gildobjanschi/ECP5_BGA381_FT2232HQ_FIFO/hdl/tx.sv

/***********************************************************************************************************************
 * Copyright (c) 2024 Virgil Dobjanschi dobjanschivirgil@gmail.com
 *
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
 * THE SOFTWARE IS PROVIDED "AS IS", WITHOUT WARRANTY OF ANY KIND, EXPRESS OR IMPLIED, INCLUDING BUT NOT LIMITED TO THE
 * WARRANTIES OF MERCHANTABILITY, FITNESS FOR A PARTICULAR PURPOSE AND NONINFRINGEMENT. IN NO EVENT SHALL THE AUTHORS
 * OR COPYRIGHT HOLDERS BE LIABLE FOR ANY CLAIM, DAMAGES OR OTHER LIABILITY, WHETHER IN AN ACTION OF CONTRACT, TORT OR
 * OTHERWISE, ARISING FROM, OUT OF OR IN CONNECTION WITH THE SOFTWARE OR THE USE OR OTHER DEALINGS IN THE SOFTWARE.
 **********************************************************************************************************************/
`timescale 1ps/1ps
`default_nettype none

`include "definitions.svh"

module tx (
    input logic reset_i,
    input logic clk_24576000_i,
    input logic clk_22579200_i,
    // Input FIFO access
    output logic rd_in_fifo_clk_o,
    output logic rd_in_fifo_en_o,
    input logic rd_in_fifo_empty_i,
    input logic [7:0] rd_in_fifo_data_i,
    // Output FIFO ports
    output logic wr_out_fifo_clk_o,
    output logic wr_out_fifo_en_o,
    output logic [7:0] wr_out_fifo_data_o,
    input logic wr_out_fifo_full_i,
    input logic wr_out_fifo_afull_i,
    output logic led_test_mode
`ifdef EXT_ENABLED
    ,
    output logic ext_led_app_in_fifo_rd_o,
    output logic ext_led_app_out_fifo_wr_o,
    output logic ext_led_app_tx_err_o,
    output logic ext_led_test_ok,
    output logic ext_led_test_fail
`endif
    );

    logic clk;
    assign clk = clk_24576000_i;

    assign rd_in_fifo_clk_o = clk;
    assign wr_out_fifo_clk_o = clk;

`ifdef EXT_ENABLED
    assign ext_led_app_in_fifo_rd_o = rd_in_fifo_en_o;
    assign ext_led_app_out_fifo_wr_o = wr_out_fifo_en_o;
`endif

`ifndef DATA_PACKETS_COUNT
    `define DATA_PACKETS_COUNT 8'd1
`endif

`ifndef DATA_PACKET_PAYLOAD
    `define DATA_PACKET_PAYLOAD 6'd63
`endif

    // State machines
    localparam STATE_IDLE       = 3'b000;
    localparam STATE_RD         = 3'b001;
    localparam STATE_WR_BUFFER  = 3'b010;
    localparam STATE_WR         = 3'b011;
    localparam STATE_ERROR      = 3'b111;
    logic [2:0] state_m;

    // Protocol state machine
    localparam STATE_FIFO_CMD       = 1'b0;
    localparam STATE_FIFO_PAYLOAD   = 1'b1;
    logic fifo_state_m;

    logic [1:0] last_fifo_cmd;
    logic data_to_send;
    logic [5:0] rd_payload_bytes;
    logic [5:0] wr_data_index;
    logic [7:0] wr_data[0:3];

`ifdef TEST_MODE
    logic [7:0] test_number;
    logic [7:0] expected_test_data;
    logic [7:0] wr_packets;
    logic [5:0] wr_payload_bytes;

    //==================================================================================================================
    // The command handler
    //==================================================================================================================
    task handle_cmd_task (input logic [1:0] fifo_cmd, input logic [5:0] payload_length);
        (* parallel_case, full_case *)
        case (fifo_cmd)
            `CMD_TEST_START: begin
`ifdef EXT_ENABLED
                ext_led_test_ok <= 1'b0;
                ext_led_test_fail <= 1'b0;
`endif

                if (payload_length == 6'd1) begin
`ifdef D_TX
                    $display ($time, "\033[0;36m TX:\t--> CMD_TEST_START. \033[0;0m");
`endif
                    // Reset the test data
                    expected_test_data <= 8'd0;
                    data_to_send <= 1'b0;

                    rd_payload_bytes <= payload_length;
                    fifo_state_m <= STATE_FIFO_PAYLOAD;
                end else begin
`ifdef D_TX
                    $display ($time, "\033[0;36m TX:\t[ERROR] --> CMD_TEST_START payload bytes: %d (expected 1). \033[0;0m", payload_length);
`endif
                    wr_data_index <= 6'd0;
                    wr_data[0] <= {`CMD_TEST_STOPPED, 6'h1};
                    wr_data[1] <= `TEST_ERROR_INVALID_START_PAYLOAD;

                    rd_in_fifo_en_o <= 1'b0;
                    state_m <= STATE_ERROR;
                end
            end

            `CMD_TEST_DATA: begin
`ifdef D_TX
                $display ($time, "\033[0;36m TX:\t--> CMD_TEST_DATA payload bytes: %d. \033[0;0m", payload_length);
`endif
                if (payload_length > 6'd0) begin
                    rd_payload_bytes <= payload_length;
                    fifo_state_m <= STATE_FIFO_PAYLOAD;
                end
            end

            `CMD_TEST_STOP: begin
                wr_data_index <= 6'd0;
                wr_data[0] <= {`CMD_TEST_STOPPED, 6'h1};
                if (payload_length == 6'd0) begin
`ifdef D_TX
                    $display ($time, "\033[0;36m TX:\t--> CMD_TEST_STOP. \033[0;0m");
`endif
                    wr_data[1] <= `TEST_ERROR_NONE;

                end else begin
`ifdef D_TX
                    $display ($time, "\033[0;36m TX:\t[ERROR] --> CMD_TEST_STOP payload bytes: %d (expected 0). \033[0;0m", payload_length);
`endif
                    wr_data[1] <= `TEST_ERROR_INVALID_STOP_PAYLOAD;
                end

                rd_in_fifo_en_o <= 1'b0;
                state_m <= STATE_ERROR;
            end

            default: begin
`ifdef D_TX
                $display ($time, "\033[0;36m TX:\t[ERROR] --> invalid command: %d. \033[0;0m", fifo_cmd);
`endif
                wr_data_index <= 6'd0;
                wr_data[0] <= {`CMD_TEST_STOPPED, 6'h1};
                wr_data[1] <= `TEST_ERROR_INVALID_CMD;

                rd_in_fifo_en_o <= 1'b0;
                state_m <= STATE_ERROR;
            end
        endcase
    endtask

    //==================================================================================================================
    // The payload handler
    //==================================================================================================================
    task handle_payload_task (input logic [1:0] fifo_cmd, input logic [7:0] fifo_data);
        (* parallel_case, full_case *)
        case (fifo_cmd)
            `CMD_TEST_START: begin
                test_number <= fifo_data;
`ifdef D_TX
                $display ($time, "\033[0;36m TX:\t--> CMD_TEST_START test number: %d. \033[0;0m", fifo_data);
`endif
                case (fifo_data)
                    `TEST_RECEIVE, `TEST_RECEIVE_SEND: begin
                    end

                    `TEST_SEND: begin
                        data_to_send <= 1'b1;
                        wr_payload_bytes <= `DATA_PACKET_PAYLOAD;
                        wr_packets <= `DATA_PACKETS_COUNT;

                        rd_in_fifo_en_o <= 1'b0;
                        state_m <= STATE_WR;
                    end

                    default: begin
                        wr_data_index <= 6'd0;
                        wr_data[0] <= {`CMD_TEST_STOPPED, 6'd2};
                        wr_data[1] <= `TEST_ERROR_INVALID_TEST_NUM;
                        wr_data[2] <= fifo_data;

                        rd_in_fifo_en_o <= 1'b0;
                        state_m <= STATE_ERROR;
                    end
                endcase
            end

            `CMD_TEST_DATA: begin
                if (fifo_data == expected_test_data) begin
`ifdef D_TX
                    $display ($time, "\033[0;36m TX:\t--> %d. \033[0;0m", fifo_data);
`endif
                    // For the loop back test write back the byte that was just received.
                    if (test_number == `TEST_RECEIVE_SEND) begin
                        // Write back the byte received
                        wr_data_index <= 6'd0;
                        wr_data[0] <= {`CMD_TEST_DATA, 6'd1};
                        wr_data[1] <= fifo_data;

                        rd_in_fifo_en_o <= 1'b0;
                        state_m <= STATE_WR_BUFFER;
                    end

                    expected_test_data <= expected_test_data + 8'd1;
                end else begin
`ifdef D_TX
                    $display ($time, "\033[0;36m TX:\t[ERROR] --> CMD_TEST_DATA invalid payload: %d (expected %d). \033[0;0m",
                                fifo_data, expected_test_data);
`endif
                    wr_data_index <= 6'd0;
                    wr_data[0] <= {`CMD_TEST_STOPPED, 6'd3};
                    wr_data[1] <= `TEST_ERROR_INVALID_TEST_DATA;
                    // Actually data received
                    wr_data[2] <= fifo_data;
                    // Expected data
                    wr_data[3] <= expected_test_data;

                    rd_in_fifo_en_o <= 1'b0;
                    state_m <= STATE_ERROR;
                end
            end

            default: begin
`ifdef D_TX
                $display ($time, "\033[0;36m TX:\t[ERROR] --> invalid command in handle_payload_task: %d. \033[0;0m", fifo_cmd);
`endif
                wr_data_index <= 6'd0;
                wr_data[0] <= {`CMD_TEST_STOPPED, 6'h1};
                wr_data[1] <= `TEST_ERROR_INVALID_LAST_CMD;

                rd_in_fifo_en_o <= 1'b0;
                state_m <= STATE_ERROR;
            end
        endcase
    endtask

    //==================================================================================================================
    // The write data handler
    //==================================================================================================================
    task write_data_task;
        if (~rd_in_fifo_empty_i) begin
            wr_out_fifo_en_o <= 1'b0;
            state_m <= STATE_RD;
        end else if (~wr_out_fifo_afull_i && ~wr_out_fifo_full_i) begin
            if (wr_payload_bytes == `DATA_PACKET_PAYLOAD) begin
                // The beginning of a packet
                wr_out_fifo_en_o <= 1'b1;
                wr_out_fifo_data_o <= {`CMD_TEST_DATA, `DATA_PACKET_PAYLOAD};
            end else if (wr_payload_bytes == 8'd0) begin
                // The end of a packet
                wr_out_fifo_en_o <= 1'b0;

                wr_packets <= wr_packets - 8'd1;
                if (wr_packets == 8'd1) begin
                    data_to_send <= 1'b0;
                    state_m <= STATE_RD;
                end else begin
                    wr_payload_bytes <= `DATA_PACKET_PAYLOAD;
                end
            end else begin
                // Send data from the packet
                wr_out_fifo_en_o <= 1'b1;
                wr_out_fifo_data_o <= expected_test_data;

                wr_payload_bytes <= wr_payload_bytes - 8'd1;
            end
`ifdef D_TX
            $display ($time, "\033[0;36m TX:\t<--: %d. \033[0;0m", expected_test_data);
`endif
            expected_test_data <= expected_test_data + 8'd1;
        end else begin
            wr_out_fifo_en_o <= 1'b0;
        end
    endtask

    //==================================================================================================================
    // The error handler
    //==================================================================================================================
    task handle_error_task;
        if (wr_data_index == 6'd0) begin
            if (wr_data[1] == `TEST_ERROR_NONE) begin
`ifdef D_TX
                $display ($time, "\033[0;36m TX:\t==== TEST OK ====. \033[0;0m");
`endif
`ifdef EXT_ENABLED
                ext_led_test_ok <= 1'b1;
`endif
            end else begin
`ifdef D_TX
                $display ($time, "\033[0;36m TX:\t==== TEST FAILED [code: %d] ====. \033[0;0m", wr_data[1]);
`endif
`ifdef EXT_ENABLED
                ext_led_test_fail <= 1'b1;
`endif
            end
        end

        write_buffer_task(STATE_IDLE);

    endtask

`else // TEST_MODE
    //==================================================================================================================
    // The command handler
    //==================================================================================================================
    task handle_cmd_task (input logic [1:0] fifo_cmd, input logic [5:0] payload_length);
/*
        (* parallel_case, full_case *)
        case (fifo_cmd)

        endcase
*/
    endtask

    //==================================================================================================================
    // The payload handler
    //==================================================================================================================
    task handle_payload_task (input logic [1:0] fifo_cmd, input logic [7:0] fifo_data);
/*
        case (fifo_cmd)

        endcase
*/
    endtask

    //==================================================================================================================
    // The error handler
    //==================================================================================================================
    task handle_error_task;
    endtask

    //==================================================================================================================
    // The write data handler
    //==================================================================================================================
    task write_data_task;
    endtask
`endif // TEST_MODE

    //==================================================================================================================
    // The FIFO reader
    //==================================================================================================================
    task read_data_task (input logic [7:0] fifo_data);
        (* parallel_case, full_case *)
        case (fifo_state_m)
            STATE_FIFO_CMD: begin
                handle_cmd_task (fifo_data[7:6], fifo_data[5:0]);
                last_fifo_cmd <= fifo_data[7:6];
            end

            STATE_FIFO_PAYLOAD: begin
                handle_payload_task (last_fifo_cmd, fifo_data);

                rd_payload_bytes <= rd_payload_bytes - 2'd1;

                if (rd_payload_bytes == 2'd1) begin
                    fifo_state_m <= STATE_FIFO_CMD;
                end
            end
        endcase
    endtask

    //==================================================================================================================
    // The FIFO writter
    //==================================================================================================================
    task write_buffer_task (input logic [2:0] next_state_m);
        if (wr_data[0][5:0] + 6'd1 == wr_data_index) begin
`ifdef D_TX
            $display ($time, "\033[0;36m TX:\t[STATE_WR_BUFFER] Done. \033[0;0m");
`endif
            wr_out_fifo_en_o <= 1'b0;
            state_m <= next_state_m;
        end else begin
            if (~wr_out_fifo_full_i && ~wr_out_fifo_afull_i) begin
`ifdef D_TX
                $display ($time, "\033[0;36m TX:\t[STATE_WR_BUFFER] <-- [%d]: %d. \033[0;0m", wr_data_index, wr_data[wr_data_index]);
`endif
                wr_out_fifo_en_o <= 1'b1;
                wr_out_fifo_data_o <= wr_data[wr_data_index];

                wr_data_index <= wr_data_index + 6'd1;
            end else begin
`ifdef D_TX
                $display ($time, "\033[0;36m TX:\tWrite buffer: Full. \033[0;0m");
`endif
                wr_out_fifo_en_o <= 1'b0;
            end
        end
    endtask

    //==================================================================================================================
    // FIFO read/write
    //==================================================================================================================
    always @(posedge clk, posedge reset_i) begin
        if (reset_i) begin
`ifdef D_TX
            $display ($time, "\033[0;36m TX:\t-- Reset. \033[0;0m");
`endif
            rd_in_fifo_en_o <= 1'b0;
            wr_out_fifo_en_o <= 1'b0;

            state_m <= STATE_RD;
            fifo_state_m <= STATE_FIFO_CMD;
            data_to_send <= 1'b0;
`ifdef TEST_MODE
            led_test_mode <= 1'b1;
`else
            led_test_mode <= 1'b0;
`endif

`ifdef EXT_ENABLED
            ext_led_app_tx_err_o <= 1'b0;
            ext_led_test_ok <= 1'b0;
            ext_led_test_fail <= 1'b0;
`endif
        end else begin
            case (state_m)
                STATE_IDLE: begin
                end

                STATE_RD: begin
                    if (~rd_in_fifo_empty_i) begin
                        // Read data out of the FIFO
                        rd_in_fifo_en_o <= 1'b1;
                        if (rd_in_fifo_en_o) begin
                            read_data_task (rd_in_fifo_data_i);
                        end
                    end else begin
                        // Stop reading
                        rd_in_fifo_en_o <= 1'b0;
                        // Go back to writting
                        if (data_to_send) begin
                            state_m <= STATE_WR;
                        end
                    end
                end

                STATE_WR: begin
                    write_data_task;
                end

                STATE_WR_BUFFER: begin
                    write_buffer_task (STATE_RD);
                end

                STATE_ERROR: begin
                    handle_error_task;
                end
            endcase
        end
    end
endmodule
